hzeller/flaschen-taschen/img/opc.png

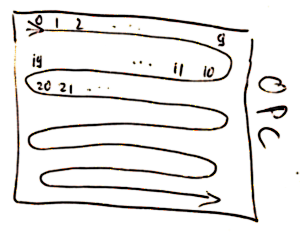
img/opc.png
