hzeller/flaschen-taschen/img/pi-adapter-sch.png

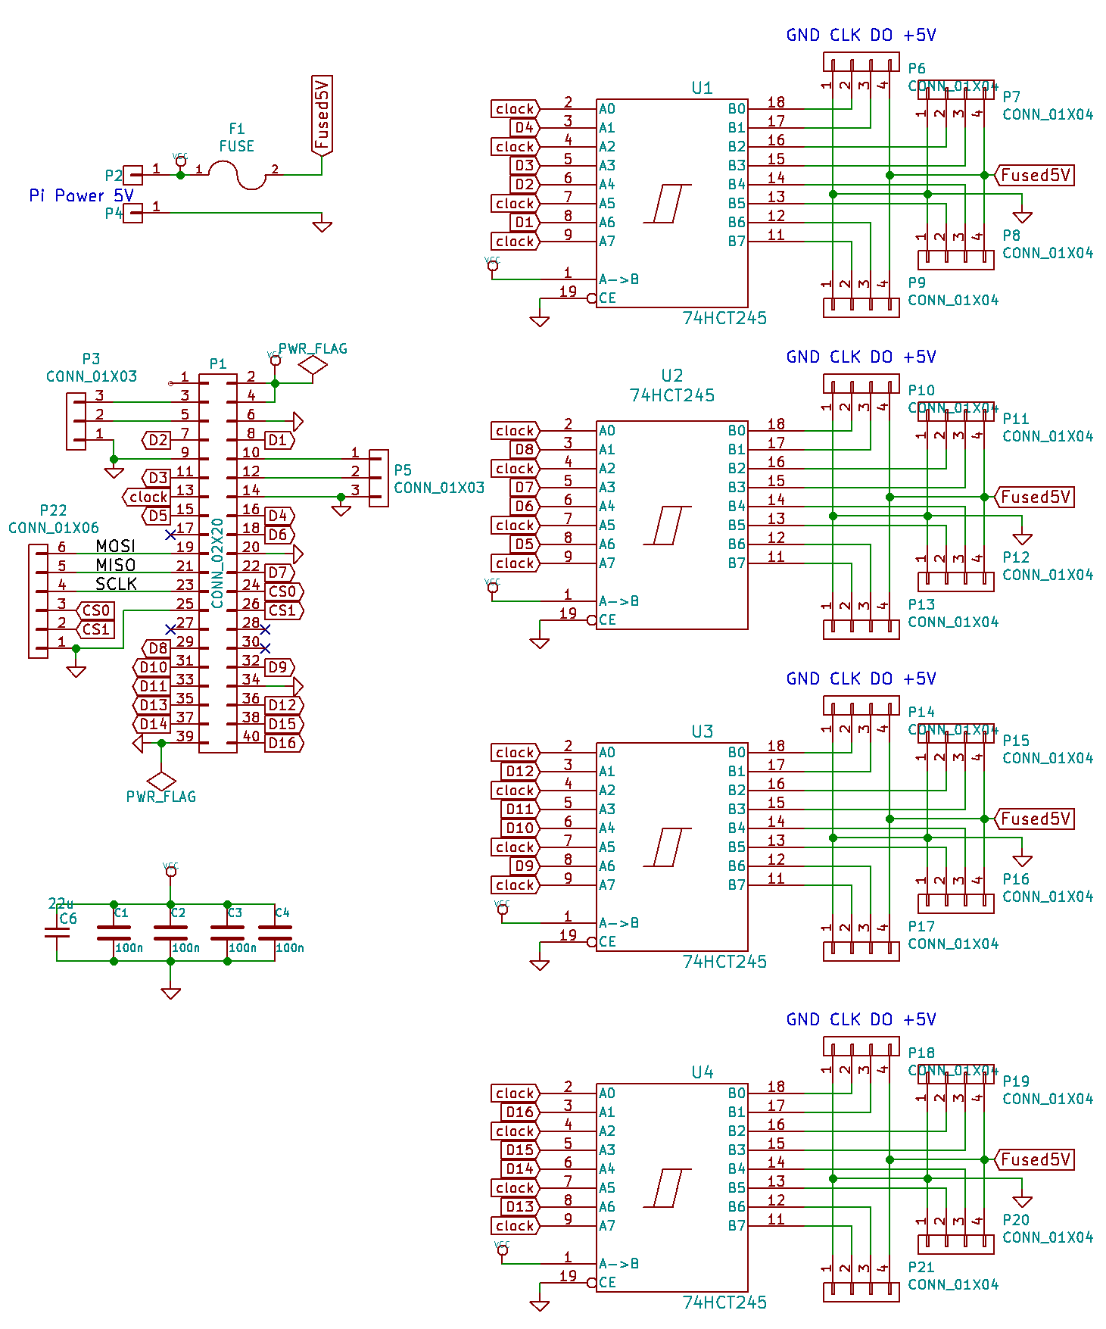
img/pi-adapter-sch.png
