hzeller/flaschen-taschen/img/power-conn.jpg

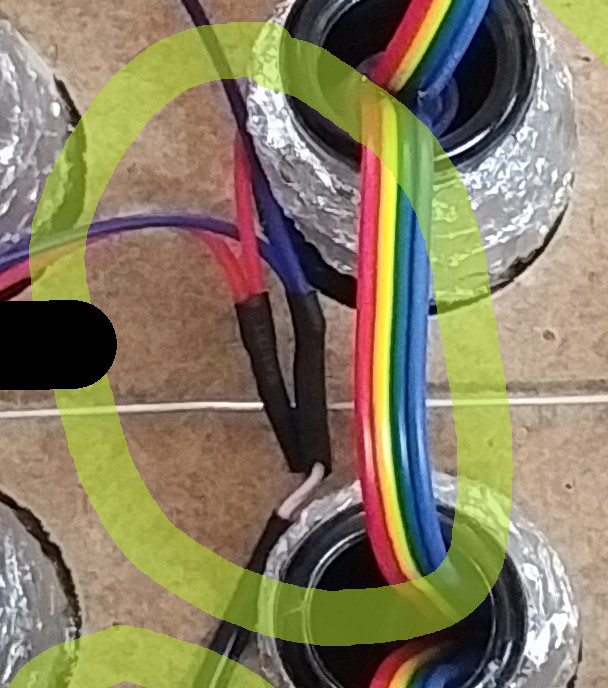
img/power-conn.jpg
