hzeller/flaschen-taschen/server/led-flaschen-taschen.h

// -*- mode: c++; c-basic-offset: 4; indent-tabs-mode: nil; -*-
//
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
#ifndef LED_FLASCHEN_TASCHEN_H_
#define LED_FLASCHEN_TASCHEN_H_

#include "flaschen-taschen.h"

#include <vector>
#include <string>

namespace spixels {
class MultiSPI;
class LEDStrip;
}

class ServerFlaschenTaschen : public FlaschenTaschen {
public:
    // Server-side FlaschenTaschen displays might need to do some initialization
    // after they have become a daemon. This can be used for general init
    // tasks, but in particular to start threads (Threads must not be started
    // before becoming a daemon).
    virtual void PostDaemonInit() {}
};

// Column helps assembling the various columns of width 5 (the width of a crate)
// to one big display. Since all SPI based strips are necessary upated in
// parallel, that SPI send command is triggered within here.
class ColumnAssembly : public ServerFlaschenTaschen {
public:
    ColumnAssembly(spixels::MultiSPI *spi);
    ~ColumnAssembly();

    // Add column. Takes over ownership of column.
    // Columns have been added right to left, or, if standing
    // behind the display: leftmost column first.
    void AddColumn(FlaschenTaschen *taschen);

    int width() const { return width_; }
    int height() const { return height_; }

    void SetPixel(int x, int y, const Color &col);
    void Send();

private:
    spixels::MultiSPI *const spi_;
    std::vector<FlaschenTaschen*> columns_;
    int width_;
    int height_;
};

// This represents one column. Unlike the final display,
// x-coordinates go right-to-left, and bottom to up.
// The final assembly will turn things around.
class CrateColumnFlaschenTaschen : public FlaschenTaschen {
public:
    // Given a simple LED strip, create a column of crates that behaves
    // the way we are snaking the strip.
    // Takes ownership of the LED strip.
    CrateColumnFlaschenTaschen(spixels::LEDStrip *strip);
    ~CrateColumnFlaschenTaschen();

    int width() const { return 5; }
    int height() const { return height_; }

    void SetPixel(int x, int y, const Color &col);
    void Send() {}  // This happens in SPI sending in ColumnAssembly

private:
    spixels::LEDStrip *strip_;
    const int height_;
};

// -- FlaschenTaschen implementation using rpi-rgb-led-matrix
namespace rgb_matrix {
class RGBMatrix;
}

class RGBMatrixFlaschenTaschen : public ServerFlaschenTaschen {
public:
    RGBMatrixFlaschenTaschen(rgb_matrix::RGBMatrix *matrix,
                             int width, int height);
    virtual ~RGBMatrixFlaschenTaschen();

    virtual void PostDaemonInit();  // Starting threads.

    int width() const { return width_; }
    int height() const { return height_; }

    void SetPixel(int x, int y, const Color &col);
    void Send() { /* update directly */ }

private:
    rgb_matrix::RGBMatrix *const matrix_;

    int width_;
    int height_;
};

class TerminalFlaschenTaschen : public ServerFlaschenTaschen {
public:
    TerminalFlaschenTaschen(int terminal_fd, int width, int heigh);
    virtual ~TerminalFlaschenTaschen();
    virtual void PostDaemonInit();

    int width() const { return width_; }
    int height() const { return height_; }

    void SetPixel(int x, int y, const Color &col);
    void Send();

protected:
    static inline void WriteByteDecimal(char *buf, uint8_t val) {
        buf[2] = (val % 10) + '0'; val /= 10;
        buf[1] = (val % 10) + '0'; val /= 10;
        buf[0] = val + '0';
    }

    const int terminal_fd_;
    const int width_;
    const int height_;
    size_t initial_offset_;
    size_t pixel_offset_;
    size_t fps_offset_;
    bool is_first_;
    std::string buffer_;
    int64_t last_time_usec_;
};

// Similar, but higher res.
class HDTerminalFlaschenTaschen : public TerminalFlaschenTaschen {
public:
    HDTerminalFlaschenTaschen(int terminal_fd, int width, int heigh);
    virtual void PostDaemonInit();

    void SetPixel(int x, int y, const Color &col);

private:
    size_t lower_row_pixel_offset_;
};

#endif // LED_FLASCHEN_TASCHEN_H_
