hzeller/flaschen-taschen/server/hd-terminal-flaschen-taschen.cc

// -*- mode: c++; c-basic-offset: 4; indent-tabs-mode: nil; -*-
//
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
#include "led-flaschen-taschen.h"

#include <stdio.h>
#include <string.h>
#include <sys/time.h>
#include <unistd.h>

#define SCREEN_CLEAR    "\033c"
#define SCREEN_PREFIX   "\033[48;2;0;0;0m"  // set black background
#define SCREEN_POSTFIX  "\033[0m"           // reset terminal settings
#define SCREEN_CURSOR_UP_FORMAT "\033[%dA"  // Move cursor up given lines.
#define CURSOR_OFF      "\033[?25l"
#define CURSOR_ON       "\033[?25h"

// Each character on the screen is divided in a top pixel and bottom pixel.
// We use the following character which fills the top block:
#define PIXEL_CHARACTER  "▀"  // Top foreground color, bottom background color

// Now, pixels on the even row will get the foreground color changed, pixels
// on odd rows the background color. Two pixels one stone. Or something.
#define ESCAPE_COLOR_FORMAT   "%03d;%03d;%03d"
#define TOP_PIXEL_COLOR       "\033[38;2;"
#define BOTTOM_PIXEL_COLOR    "\033[48;2;"

// Displaying the framerate at the bottom of the screen. Keep spaceholder.
#define FPS_PLACEHOLDER "___________"
#define FPS_BACKSPACE   "\b\b\b\b\b\b\b\b\b\b\b"

HDTerminalFlaschenTaschen::HDTerminalFlaschenTaschen(int fd, int w, int h)
    // Height is rounded up to the next even number.
    : TerminalFlaschenTaschen(fd, w, (h + 1) & ~0x1) {
}

void HDTerminalFlaschenTaschen::PostDaemonInit() {
    buffer_.append(SCREEN_PREFIX);
    initial_offset_ = buffer_.size();
    char scratch[64];
    snprintf(scratch, sizeof(scratch),
             TOP_PIXEL_COLOR    ESCAPE_COLOR_FORMAT "m"
             BOTTOM_PIXEL_COLOR ESCAPE_COLOR_FORMAT "m"
             PIXEL_CHARACTER,
             0, 0, 0, 0, 0, 0); // black.
    pixel_offset_ = strlen(scratch);
    for (int y = 0; y < height_ / 2; ++y) {
        for (int x = 0; x < width_; ++x) {
            buffer_.append(scratch);
        }
        buffer_.append("\n");
    }

    buffer_.append(SCREEN_POSTFIX);

    fps_offset_ = buffer_.size();
    buffer_.append(FPS_PLACEHOLDER FPS_BACKSPACE);

    snprintf(scratch, sizeof(scratch), SCREEN_CURSOR_UP_FORMAT, height_/2);
    buffer_.append(scratch);

    // Some useful precalculated length.
    snprintf(scratch, sizeof(scratch),
             ESCAPE_COLOR_FORMAT "m" BOTTOM_PIXEL_COLOR, 0, 0, 0);
    lower_row_pixel_offset_ = strlen(scratch);
}

void HDTerminalFlaschenTaschen::SetPixel(int x, int y, const Color &col) {
    if (x < 0 || x >= width_ || y < 0 || y >= height_) return;
    const int double_row = y/2;
    const int pos = initial_offset_
        + (width_ * double_row + x) * pixel_offset_
        + strlen(TOP_PIXEL_COLOR)            // go where the color fmt starts
        + (y % 2) * lower_row_pixel_offset_  // offset for odd-row y-pixels
        + double_row;                        // 1 newline per double row
    char *buf = const_cast<char*>(buffer_.data()) + pos;  // Living on the edge
    WriteByteDecimal(buf, col.r);      // rrr;___;___
    WriteByteDecimal(buf + 4, col.g);  // ___;ggg;___
    WriteByteDecimal(buf + 8, col.b);  // ___;___;bbb
}
