hzeller/flaschen-taschen/server/flaschen-taschen.h

// -*- mode: c++; c-basic-offset: 4; indent-tabs-mode: nil; -*-
//
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
#ifndef FLASCHEN_TASCHEN_H_
#define FLASCHEN_TASCHEN_H_

#include <stdint.h>

struct Color {
    Color() {}
    Color(int rr, int gg, int bb) : r(rr), g(gg), b(bb){}

    uint8_t r;
    uint8_t g;
    uint8_t b;
};

// We use multiple hardware implementations for FlaschenTaschen. This
// is the general interface.
class FlaschenTaschen {
public:
    virtual ~FlaschenTaschen(){}

    virtual int width() const = 0;
    virtual int height() const = 0;

    virtual void SetPixel(int x, int y, const Color &col) = 0;
    virtual void Send() = 0;
};

class StackedFlaschenTaschen : public FlaschenTaschen {
public:
    StackedFlaschenTaschen(FlaschenTaschen *top, FlaschenTaschen *bottom)
        : top_(top), bottom_(bottom) {
    }

    int width() const { return top_->width(); }
    int height() const { return top_->height() + bottom_->height(); }

    void SetPixel(int x, int y, const Color &col) {
        if (y >= top_->height()) {
            bottom_->SetPixel(x, y - top_->height(), col);
        } else {
            top_->SetPixel(x, y, col);
        }
    }

    void Send() {
        top_->Send();
        bottom_->Send();
    }

private:
    FlaschenTaschen *const top_;
    FlaschenTaschen *const bottom_;
};

// Needs to be connected to GPIO 18 (pin 12 on RPi header)
class WS2811FlaschenTaschen : public FlaschenTaschen {
public:
    WS2811FlaschenTaschen(int width, int height);
    virtual ~WS2811FlaschenTaschen();

    int width() const { return width_; }
    int height() const { return height_; }

    void SetPixel(int x, int y, const Color &col);
    void Send();

private:
    const int width_;
    const int height_;
};

// CLK is GPIO 17 (RPI header pin 11). Rest of pin user chosen.
class LPD6803FlaschenTaschen : public FlaschenTaschen {
public:
    LPD6803FlaschenTaschen(int gpio, int width, int height);
    virtual ~LPD6803FlaschenTaschen();

    int width() const { return width_; }
    int height() const { return height_; }

    void SetPixel(int x, int y, const Color &col);
    void Send();

    void SetColorCorrect(float r, float g, float b) {
        r_correct = r; g_correct = g; b_correct = b;
    }
private:
    const int gpio_pin_;
    const int width_;
    const int height_;
    float r_correct, g_correct, b_correct;
};

#endif // FLASCHEN_TASCHEN_H_
