hzeller/flaschen-taschen/server/opc-server.cc

// -*- mode: cc; c-basic-offset: 4; indent-tabs-mode: nil; -*-
//
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
// Receives http://openpixelcontrol.org/ and updates display.

#include <errno.h>
#include <stdint.h>
#include <stdio.h>
#include <string.h>
#include <sys/socket.h>
#include <sys/types.h>
#include <unistd.h>
#include <netinet/in.h>
#include <arpa/inet.h>
#include <sys/time.h>

#include "flaschen-taschen.h"
#include "ft-thread.h"
#include "servers.h"

#define SHOW_REFRESH_RATE 0

struct Header {
    uint8_t y_pos;
    uint8_t command;
    uint8_t size_hi;
    uint8_t size_lo;
};

static bool reliable_read(int fd, void *buf, size_t count) {
    ssize_t r;
    while ((r = read(fd, buf, count)) > 0) {
        count -= r;
        buf = (char*)buf + r;
    }
    return count == 0;
}

// Open server. Return file-descriptor or -1 if listen fails.
static int open_server(int port) {
    if (port > 65535) {
        fprintf(stderr, "OPC: Invalid port %d\n", port);
        return -1;
    }
    int s = socket(AF_INET6, SOCK_STREAM, 0);
    if (s < 0) {
        fprintf(stderr, "OPC: creating socket: %s", strerror(errno));
        return -1;
    }

    struct sockaddr_in6 addr = {0};
    addr.sin6_family = AF_INET6;
    addr.sin6_addr = in6addr_any;
    addr.sin6_port = htons(port);
    int sock_opt = 1;
    setsockopt(s, SOL_SOCKET, SO_REUSEADDR, &sock_opt, sizeof(sock_opt));

    sock_opt = 0;
    setsockopt(s, IPPROTO_IPV6, IPV6_V6ONLY, &sock_opt, sizeof(sock_opt));
    if (bind(s, (struct sockaddr *) &addr, sizeof(addr)) < 0) {
        fprintf(stderr, "OPC: Trouble binding to port %d: %s",
                port, strerror(errno));
        return -1;
    }
    return s;
}

static void handle_connection(int fd, FlaschenTaschen *display,
                              ft::Mutex *mutex) {
    bool any_error = false;
    while (!any_error) {
#if SHOW_REFRESH_RATE
        struct timeval start, end;
        gettimeofday(&start, NULL);
#endif

        struct Header h;
        if (!reliable_read(fd, &h, sizeof(h)))
            break;  // lazily assume that we get enough.
        uint16_t size = (uint16_t) h.size_hi << 8 | h.size_lo;
        uint8_t *buffer = new uint8_t[ size ];
        if (!reliable_read(fd, buffer, size))
            any_error = true;
        int leds = size / 3;
        uint8_t *pixel_pos = buffer;
        mutex->Lock();
        for (int x = 0; x < leds; ++x) {
            Color c;
            c.r = *pixel_pos++;
            c.g = *pixel_pos++;
            c.b = *pixel_pos++;

            // Ideally, we'd think that we can have the channel denote the
            // y-axis, then x-axis is the pixel.
            //display->SetPixel(x, h.y_pos, c);

            // .. However OPC seems to be in the mindset that a display
            // is essentially a single, gigantically back and forth
            // wrapped strip. At least in the default 'wall' configuration.
            // Lets accomodate that.
            const int col = x % display->width();
            const int row = x / display->width();
            display->SetPixel(row % 2 == 0 ? col : display->width() - col - 1,
                              row, c);
        }
        display->Send();
        mutex->Unlock();
        delete [] buffer;
#if SHOW_REFRESH_RATE
        gettimeofday(&end, NULL);
        int64_t usec = ((uint64_t)end.tv_sec * 1000000 + end.tv_usec)
            - ((int64_t)start.tv_sec * 1000000 + start.tv_usec);
        printf("\b\b\b\b\b\b\b\b%6.1fHz", 1e6 / usec);
#endif
    }
}

static void run_server(int listen_socket,
                       FlaschenTaschen *display, ft::Mutex *mutex) {
    if (listen(listen_socket, 2) < 0) {
        fprintf(stderr, "OPC: listen() failed: %s", strerror(errno));
        return;
    }
    
    for (;;) {
        struct sockaddr_in client;
        socklen_t socklen = sizeof(client);
        int fd = accept(listen_socket, (struct sockaddr*) &client, &socklen);
        if (fd < 0) return;
        handle_connection(fd, display, mutex);
    }

    close(listen_socket);
}

// public interface
static int server_socket = -1;
bool opc_server_init(int port) {
    server_socket = open_server(port);
    if (server_socket < 0) {
        perror("Listening on opc socket");
        return false;
    }
    fprintf(stderr, "OPC server ready to listen on %d\n", port);
    return true;
}

class OPCThread : public ft::Thread {
public:
    OPCThread(FlaschenTaschen *display, ft::Mutex *mutex)
        : display_(display), mutex_(mutex) {}

    virtual void Run() {
        run_server(server_socket, display_, mutex_);
    }

private:
    FlaschenTaschen *const display_;
    ft::Mutex *const mutex_;
};

void opc_server_run_thread(FlaschenTaschen *display, ft::Mutex *mutex) {
    OPCThread *thread = new OPCThread(display, mutex);
    thread->Start();
}
